irudoy/cansult/firmware/scripts/can_capture.py

#!/usr/bin/env python3
"""Capture CAN frames for a fixed duration. Atomic: open, capture, close.

Optionally send a CAN command before capturing (PRE_CMD).
"""

import argparse
import sys
import time
import can
from can.interfaces.pcan.basic import PCANBasic, PCAN_USBBUS1

STATES = ['STARTUP', 'INIT', 'POST_INIT', 'WAITING', 'IDLE', 'STREAMING']

CANSULT_IDS = {0x665, 0x666, 0x667, 0x668, 0x669, 0x66A, 0x66B, 0x66F}


def decode_0x665(d, _prev):
    state = STATES[d[0]] if d[0] < len(STATES) else str(d[0])
    def r(val):
        return f'{val}{"+" if val == 255 else ""}'
    return (f'DIAG  {state:10s} ORE={r(d[1])}/s IMPL={r(d[2])}/s '
            f'CAN={r(d[3])}/s DMA={d[4]} WDT={d[5]} rc={d[6]} ms={d[7]*4}')


def decode_0x666(d):
    return (f'DATA1 bat={d[0]*0.08:.1f}V cool={d[1]-50}C ign={110-d[2]}deg '
            f'O2={d[3]*10}mV TPS={d[4]*20}mV AAC={d[5]/2:.0f}% '
            f'AF={d[6]}% AF_sl={d[7]}%')


def decode_0x667(d):
    rpm = (d[1] * 256 + d[2]) * 12.5
    inj = (d[3] * 256 + d[4]) / 100.0
    maf = (d[5] * 256 + d[6]) * 5
    return (f'DATA2 spd={d[0]*2}km/h rpm={rpm:.0f} '
            f'inj={inj:.2f}ms MAF={maf}mV')


def decode_0x668(d):
    return (f'DATA3 bit1=0x{d[0]:02X} bit2=0x{d[1]:02X} '
            f'Vdev={d[2]*0.08:.1f}V DTC=0x{d[6]:02X} hb={d[7]}')


CAN_STATE_NAMES = {
    0: 'RESET', 1: 'READY', 2: 'LISTENING',
    3: 'SLEEP_P', 4: 'SLEEP_A', 5: 'ERROR',
}


def decode_0x66b(d):
    fe = (d[0] << 8) | d[1]
    ne = (d[2] << 8) | d[3]
    temp_raw = (d[4] << 8) | d[5]
    temp = temp_raw - 0x10000 if temp_raw & 0x8000 else temp_raw
    can_recov = d[6]
    run_mode = 'ADAPTER' if d[7] & 0x80 else 'STREAM'
    can_state = CAN_STATE_NAMES.get(d[7] & 0x7F, f'?{d[7] & 0x7F}')
    return (f'DIAG2 FE={fe} NE={ne} T={temp/10:.1f}C '
            f'can_recov={can_recov} can_state={can_state} mode={run_mode}')


def decode_debug(can_id, d, dlc):
    direction = 'RX' if can_id == 0x669 else 'TX'
    hexdata = ' '.join(f'{b:02X}' for b in d[:dlc])
    return f'DBG-{direction} [{dlc}] {hexdata}'


def format_msg(msg, prev_diag):
    d = msg.data
    aid = msg.arbitration_id
    if aid == 0x665:
        text = decode_0x665(d, prev_diag)
        return text, prev_diag
    elif aid == 0x666:
        return decode_0x666(d), prev_diag
    elif aid == 0x667:
        return decode_0x667(d), prev_diag
    elif aid == 0x668:
        return decode_0x668(d), prev_diag
    elif aid == 0x66B:
        return decode_0x66b(d), prev_diag
    elif aid in (0x669, 0x66A):
        return decode_debug(aid, d, msg.dlc), prev_diag
    else:
        hexdata = ' '.join(f'{b:02X}' for b in d[:msg.dlc])
        return f'0x{aid:03X} [{msg.dlc}] {hexdata}', prev_diag


def main():
    parser = argparse.ArgumentParser(description='Capture CAN frames for a fixed duration')
    parser.add_argument('--channel', default='PCAN_USBBUS1')
    parser.add_argument('--bitrate', type=int, default=500000)
    parser.add_argument('--duration', type=float, default=3.0, help='Capture duration in seconds')
    parser.add_argument('--ids', help='Filter CAN IDs, e.g. 0x665,0x669,0x66A')
    parser.add_argument('--cansult', action='store_true', help=f'Filter to cansult IDs: {", ".join(f"0x{i:03X}" for i in sorted(CANSULT_IDS))}')
    parser.add_argument('--pre-cmd', help='Send CAN frame before capture, e.g. "0x66F 01"')
    args = parser.parse_args()

    id_filter = None
    if args.ids:
        id_filter = set(int(x, 0) for x in args.ids.split(','))
    elif args.cansult:
        id_filter = CANSULT_IDS

    # Clean up any previous PCAN state
    pcan = PCANBasic()
    pcan.Uninitialize(PCAN_USBBUS1)

    bus = can.Bus(interface='pcan', channel=args.channel, bitrate=args.bitrate)
    try:
        # Send pre-command if specified
        if args.pre_cmd:
            parts = args.pre_cmd.split()
            can_id = int(parts[0], 0)
            data = bytes(int(b, 16) for b in parts[1:])
            bus.send(can.Message(arbitration_id=can_id, data=data, is_extended_id=False))
            time.sleep(0.05)  # let the command take effect

        # Capture
        prev_diag = None
        count = 0
        deadline = time.time() + args.duration

        while time.time() < deadline:
            remaining = deadline - time.time()
            msg = bus.recv(timeout=min(remaining, 0.5))
            if msg is None:
                continue
            if id_filter is not None and msg.arbitration_id not in id_filter:
                continue

            text, prev_diag = format_msg(msg, prev_diag)
            ts = time.strftime('%H:%M:%S')
            print(f'{ts} {text}', flush=True)
            count += 1

        print(f'--- {count} frames in {args.duration}s ---')
    finally:
        bus.shutdown()
        pcan.Uninitialize(PCAN_USBBUS1)


if __name__ == '__main__':
    main()
